centech/LED-Control-Panel/images/box29.jpg

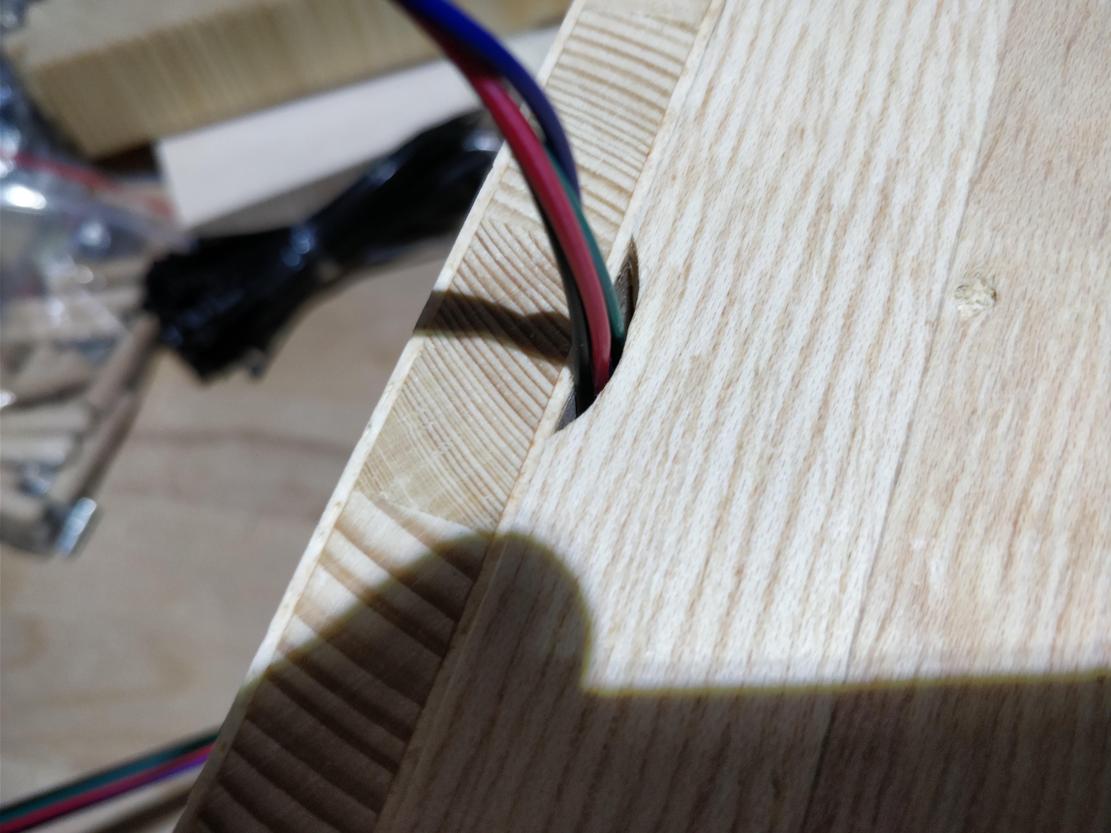
images/box29.jpg
