centech/LED-Control-Panel/images/box30.jpg

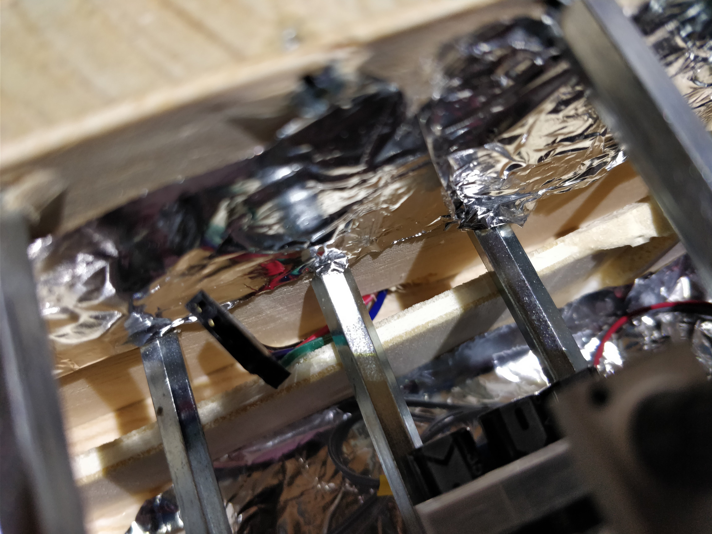
images/box30.jpg
